harbaum/LCD2USB/circuit/pcb.png

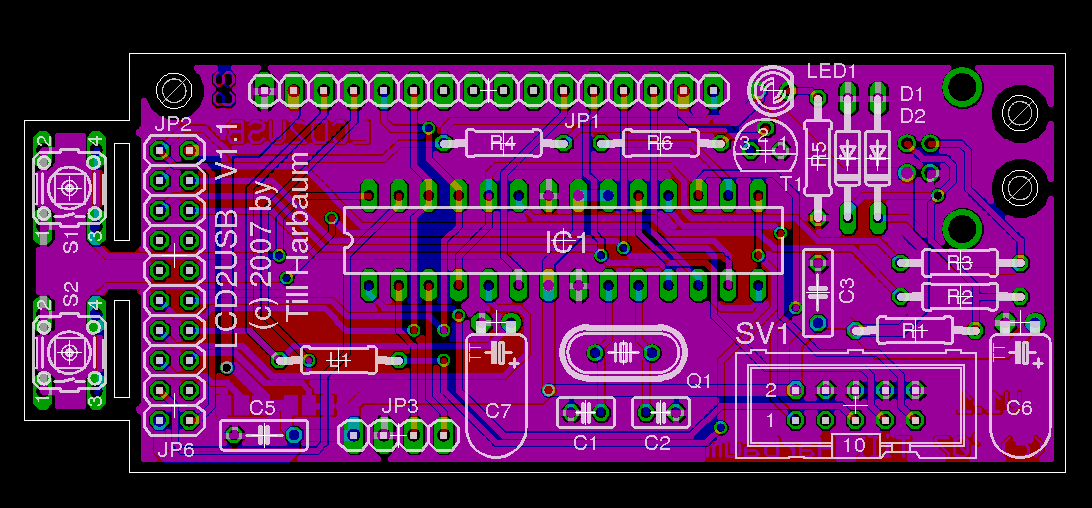
circuit/pcb.png
